dimitri-rebrikov/rainradar/doc/assembly/esp32.jpg

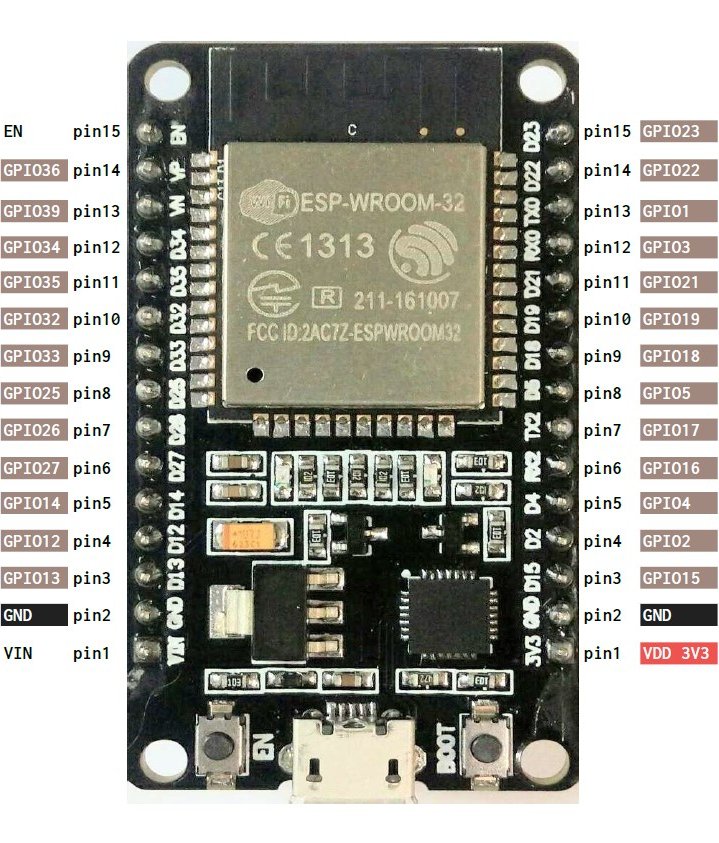
doc/assembly/esp32.jpg
