dimitri-rebrikov/rainradar/doc/assembly/led_matrix.png

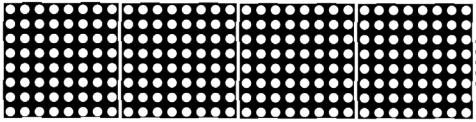
doc/assembly/led_matrix.png
