dimitri-rebrikov/rainradar/doc/manual/rainradar_connected.jpg

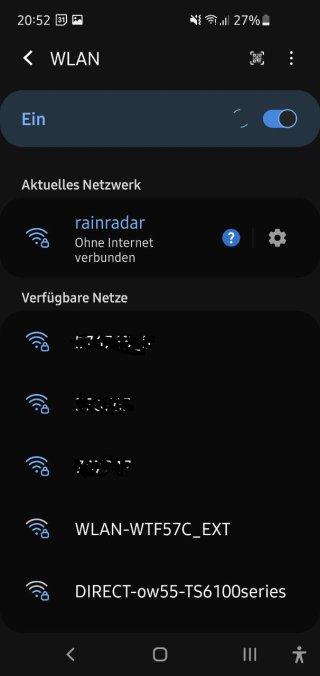
doc/manual/rainradar_connected.jpg
