dimitri-rebrikov/rainradar/rainradar/dnsquery.py

# from https://github.com/amora-labs/micropython-captive-portal/blob/master/captive.py
class DNSQuery:
  def __init__(self, data):
    self.data=data
    self.dominio=''

    m = data[2] # ord(data[2])
    tipo = (m >> 3) & 15   # Opcode bits
    if tipo == 0:                     # Standard query
      ini=12
      lon=data[ini] # ord(data[ini])
      while lon != 0:
        self.dominio+=data[ini+1:ini+lon+1].decode("utf-8") +'.'
        ini+=lon+1
        lon=data[ini] #ord(data[ini])

  def respuesta(self, ip):
    packet=b''
    if self.dominio:
      packet+=self.data[:2] + b"\x81\x80"
      packet+=self.data[4:6] + self.data[4:6] + b'\x00\x00\x00\x00'   # Questions and Answers Counts
      packet+=self.data[12:]                                         # Original Domain Name Question
      packet+= b'\xc0\x0c'                                             # Pointer to domain name
      packet+= b'\x00\x01\x00\x01\x00\x00\x00\x3c\x00\x04'             # Response type, ttl and resource data length -> 4 bytes
      packet+=bytes(map(int,ip.split('.'))) # 4 bytes of IP
    return packet
