dimitri-rebrikov/rainradar/rainradar/unquote.py

# adapted from https://raw.githubusercontent.com/lucien2k/wipy-urllib/master/urllib.py

def unquote(s):
    """Kindly rewritten by Damien from Micropython"""
    """No longer uses caching because of memory limitations"""
    res = s.split('%')
    for i in range(1, len(res)):
        item = res[i]
        try:
            res[i] = chr(int(item[:2], 16)) + item[2:]
        except ValueError:
            res[i] = '%' + item
    return "".join(res)

def unquote_plus(s):
    """unquote('%7e/abc+def') -> '~/abc def'"""
    s = s.replace('+', ' ')
    return unquote(s)
